HanYangZhao/ultrasonic-trombone/photos/IMG_2274.JPG

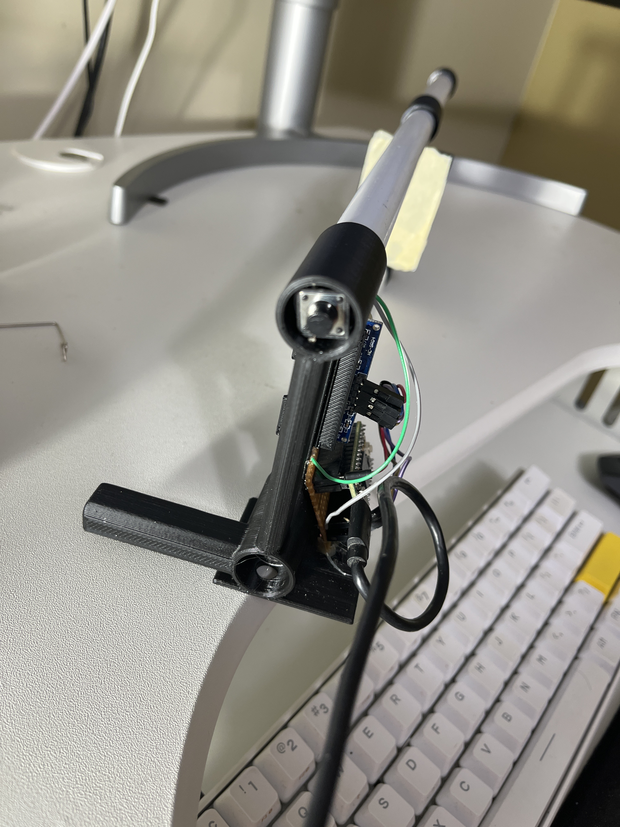
photos/IMG_2274.JPG
